Sn3akySqu1d/Soundalyser/Images/image-100.png

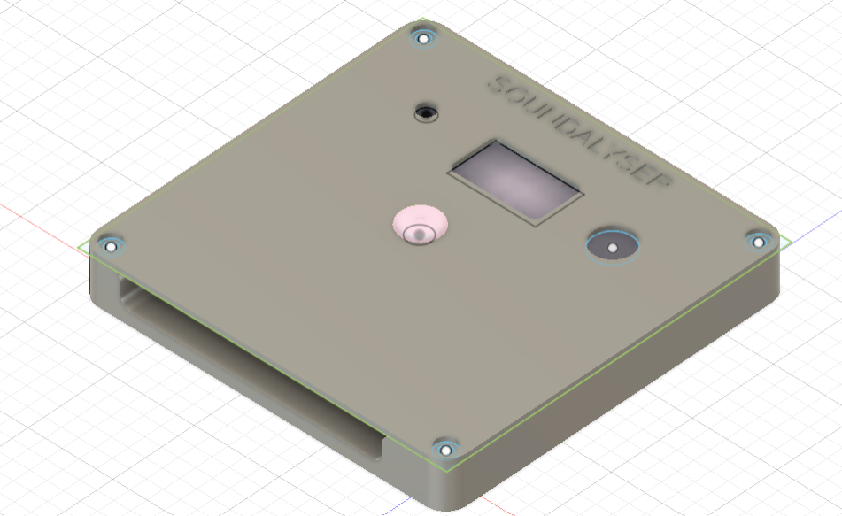
Images/image-100.png
